bcancinov/mdc-power-p6-umodule/sim/LTM4653.asc

@1: fra; delay=2m fstart=2.1875K fend=560K oct=2 fcoarse=17.5K pp0=192m pp1=12m f0=2.1875K f1=35K tavgmin=50µ tsettle=28.5714µ
C1: cap; 22µ; Rser=40m Lser=1.7n
C2: cap; 4.7µ
C3: cap; 2.4n
C4: cap; 4.7µ
C5: cap; 10p
Coc1: cap; 39.162µ; x4; Rser=2.17m Lser=0.2n
I2: current; PWL(0 0 2m 0 2.00001m 1)
R1: res; 62k
R2: res; 120k
R3: res; 24
R4: res; 0.5
R5: res; 8.87k
R6: res; 100K
R7: res; 44.2k
R8: res; '6/0.01'
U2: LTM4653
V1: voltage; 12
V2: voltage; PULSE(0 3.3 0 1e-9 1e-9 0.25e-6 0.5e-6)
Named nets: 0, OUT, IN, clk
.tran 2.5m startup
.fra startup
